miksrv/arduino-weather-station/models/sensors-holder/sensors_holder_arm_X2.jpg

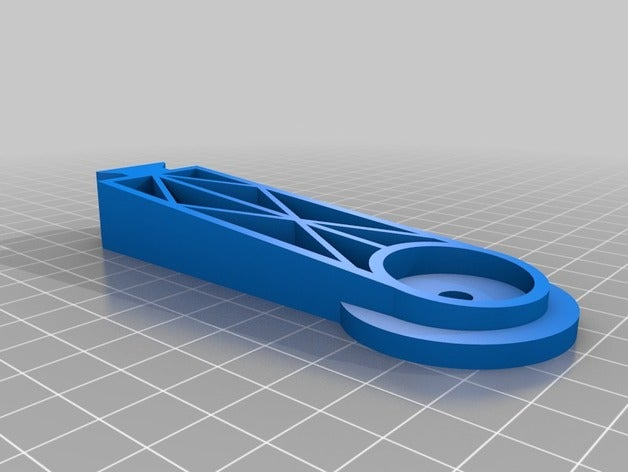
models/sensors-holder/sensors_holder_arm_X2.jpg
