miksrv/arduino-weather-station/models/sensors-holder/sensors_holder_center.jpg

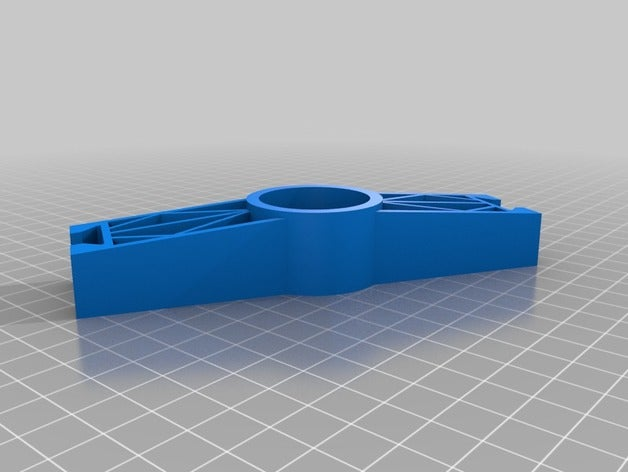
models/sensors-holder/sensors_holder_center.jpg
