miksrv/arduino-weather-station/models/wind-direction/arrow.jpg

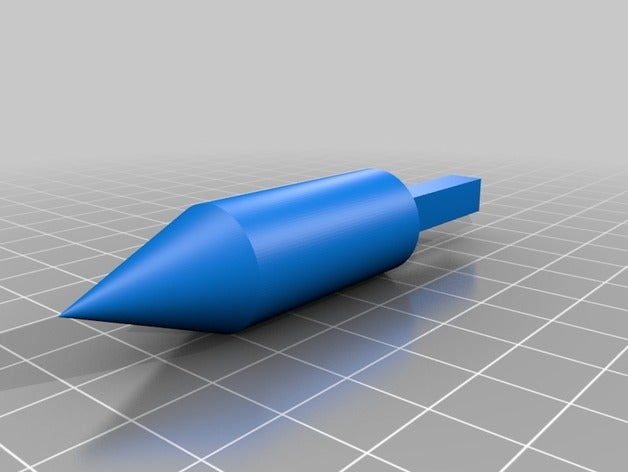
models/wind-direction/arrow.jpg
