miksrv/arduino-weather-station/models/wind-direction/body.jpg

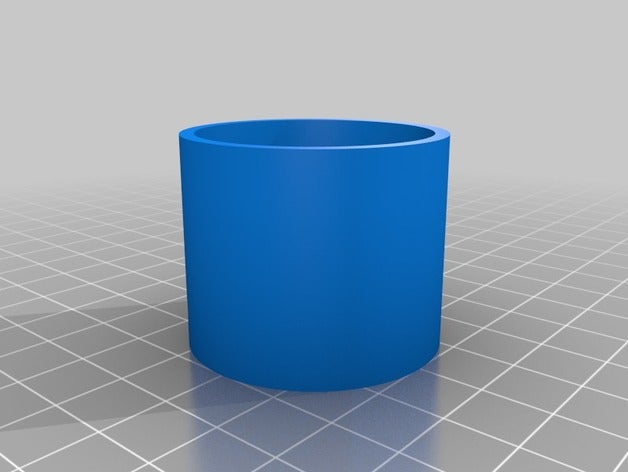
models/wind-direction/body.jpg
