miksrv/arduino-weather-station/models/wind-direction/bottom.jpg

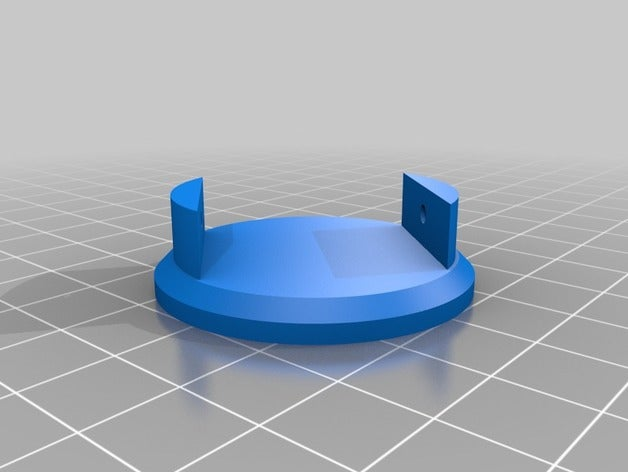
models/wind-direction/bottom.jpg
