miksrv/arduino-weather-station/models/wind-direction/sensor_holder.jpg

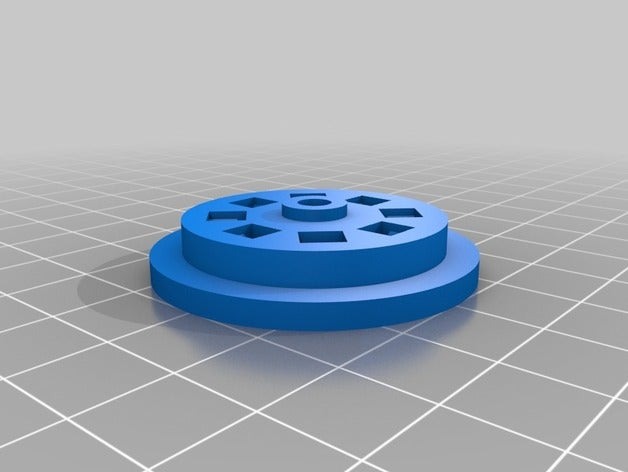
models/wind-direction/sensor_holder.jpg
