miksrv/arduino-weather-station/models/wind-direction/top.jpg

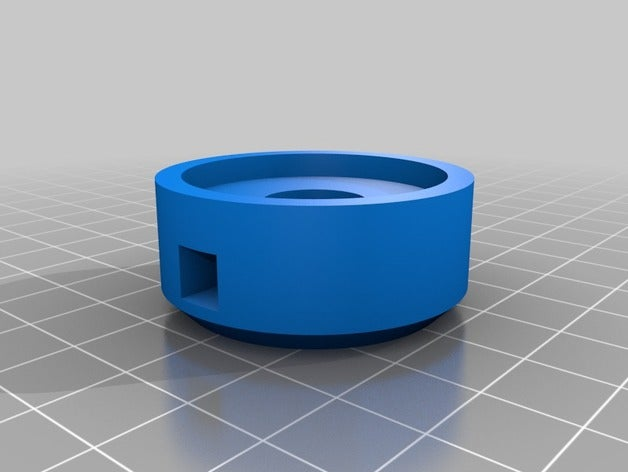
models/wind-direction/top.jpg
